lademeister/Bicker-UPSIC-1205_decoder_and_NUT-server_ESP32_C3/Images Bicker UPSIC-1205 usage/OLED_and_LED_Bargraph_SOC78.jpg

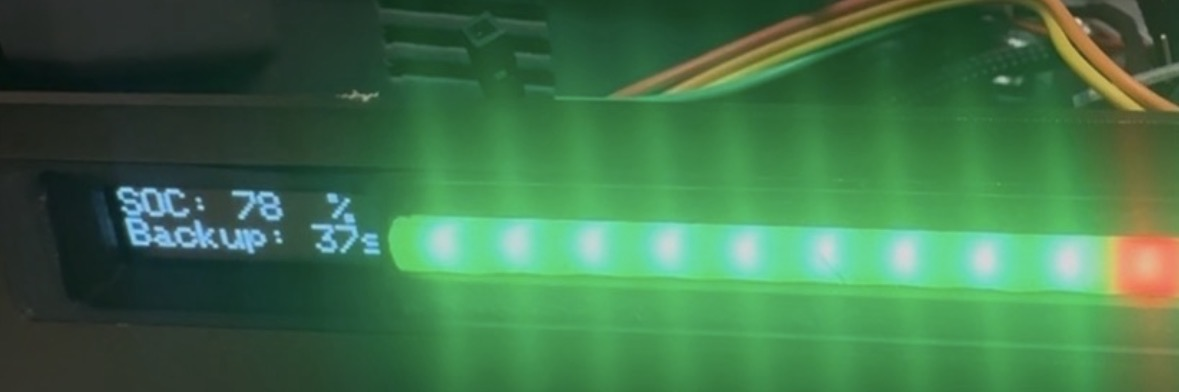
Images Bicker UPSIC-1205 usage/OLED_and_LED_Bargraph_SOC78.jpg
