lademeister/Bicker-UPSIC-1205_decoder_and_NUT-server_ESP32_C3/Bicker_UPSIC1205_ESP32-NUT-Server_without_PSZ-1063_V9.4_C3_Github/ha_discovery.h

#ifndef HA_DISCOVERY_H
#define HA_DISCOVERY_H

#include <Arduino.h>
#include <PubSubClient.h>

class HADiscovery
{
public:

    void begin(PubSubClient &client);

    void publish();

private:

    PubSubClient *mqtt;

    void publishSensor(
        const char *id,
        const char *name,
        const char *unit,
        const char *deviceClass,
        const char *stateClass,
        const char *icon
    );

    bool published = false;
};

#endif
