lademeister/Bicker-UPSIC-1205_decoder_and_NUT-server_ESP32_C3/Bicker_UPSIC1205_ESP32-NUT-Server_without_PSZ-1063_V9.4_C3_Github/wifi_setup.h

#ifndef WIFI_SETUP_H
#define WIFI_SETUP_H

#include <Arduino.h>
#include <WiFi.h>
#include "config.h"


class WiFiManagerESP
{

public:

  void begin();


  void loop();


  String getIP();



private:

  bool connected = false;


};


#endif
